WildernessLabs/Apiarium/Design/Sketches/Hive.png

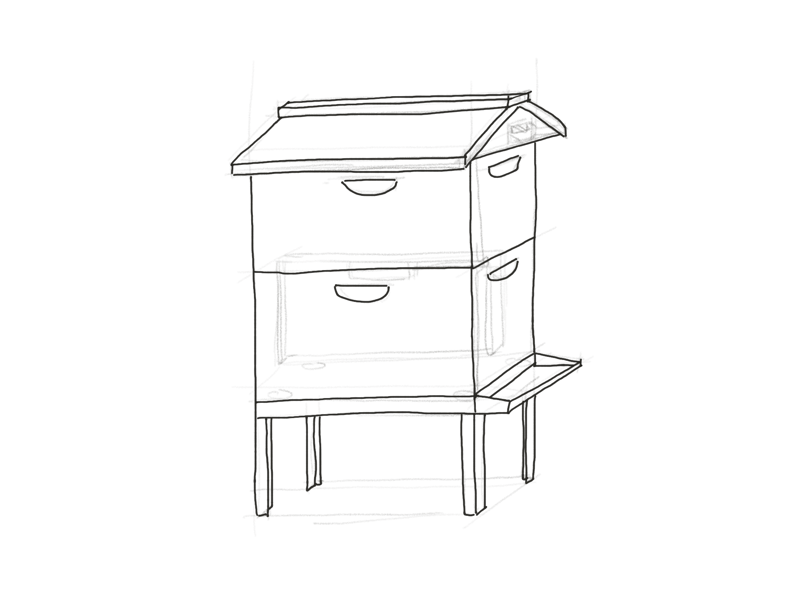
Design/Sketches/Hive.png
