WildernessLabs/Apiarium/Documentation/Photos/Enclosure_Bottom.jpg

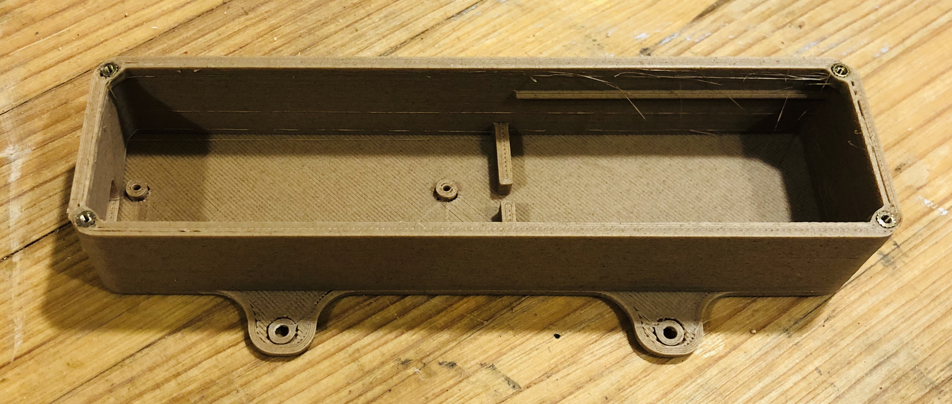
Documentation/Photos/Enclosure_Bottom.jpg
