WildernessLabs/Apiarium/Documentation/Photos/Enclosure_Lid.jpg

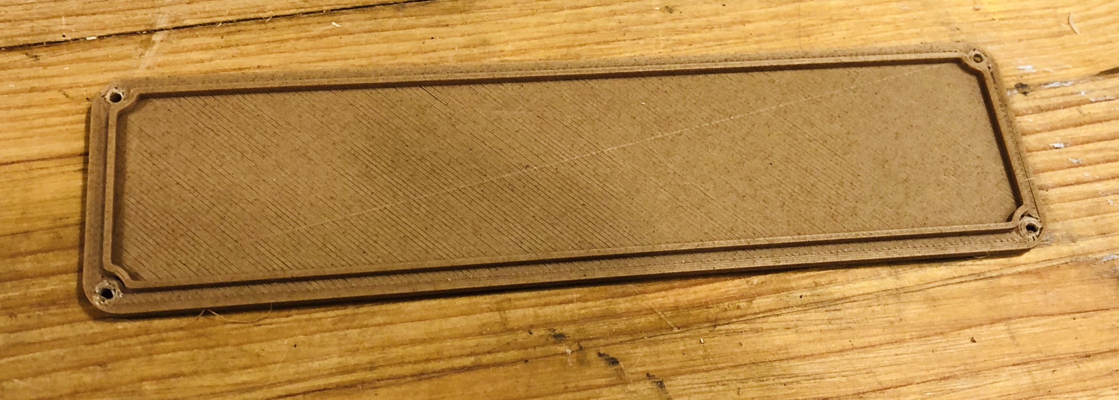
Documentation/Photos/Enclosure_Lid.jpg
