WildernessLabs/Apiarium/Documentation/Photos/M2_Heat-Set_Inserts.jpg

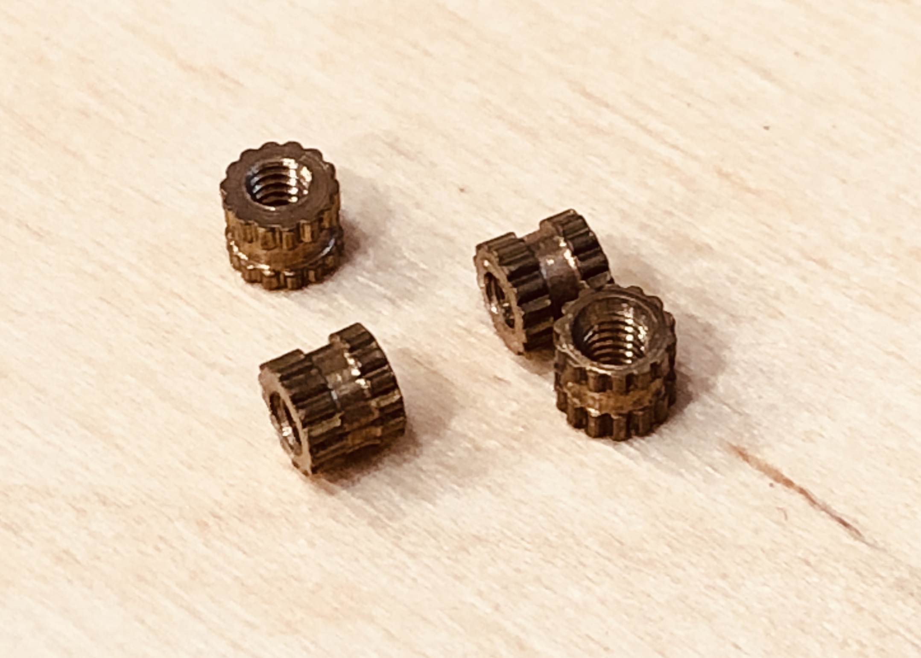
Documentation/Photos/M2_Heat-Set_Inserts.jpg
