WildernessLabs/Apiarium/Documentation/Photos/M2x4mm_Socket_Screws.jpg

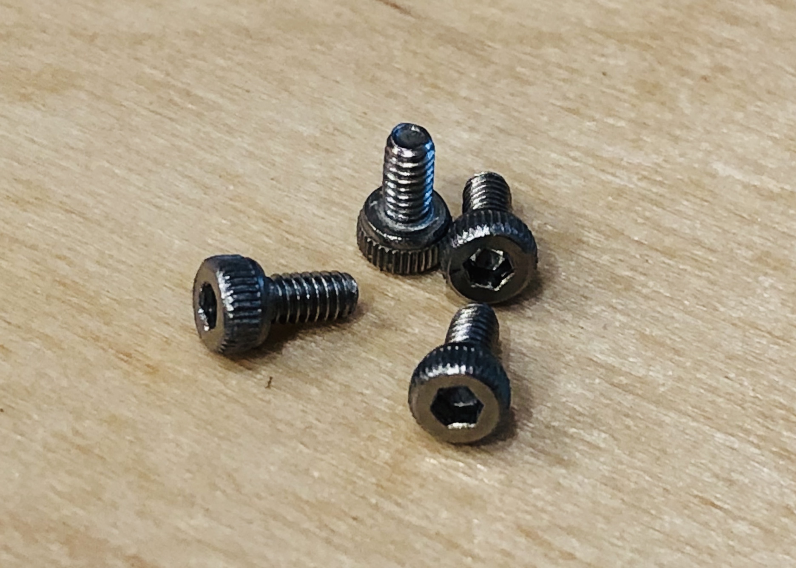
Documentation/Photos/M2x4mm_Socket_Screws.jpg
