WildernessLabs/Apiarium/Documentation/Photos/Meadow.jpg

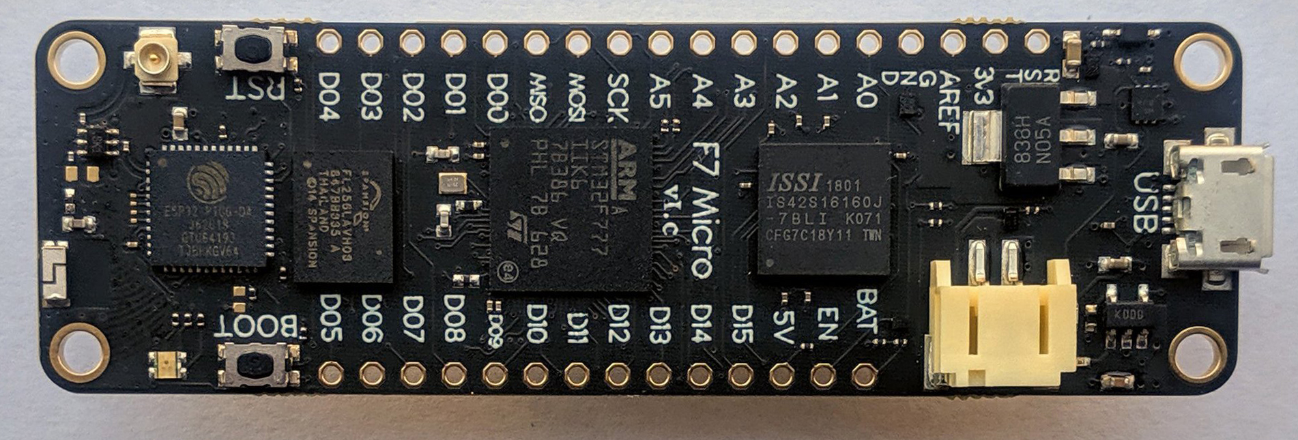
Documentation/Photos/Meadow.jpg
