WildernessLabs/Apiarium/Documentation/Photos/Si7021.jpg

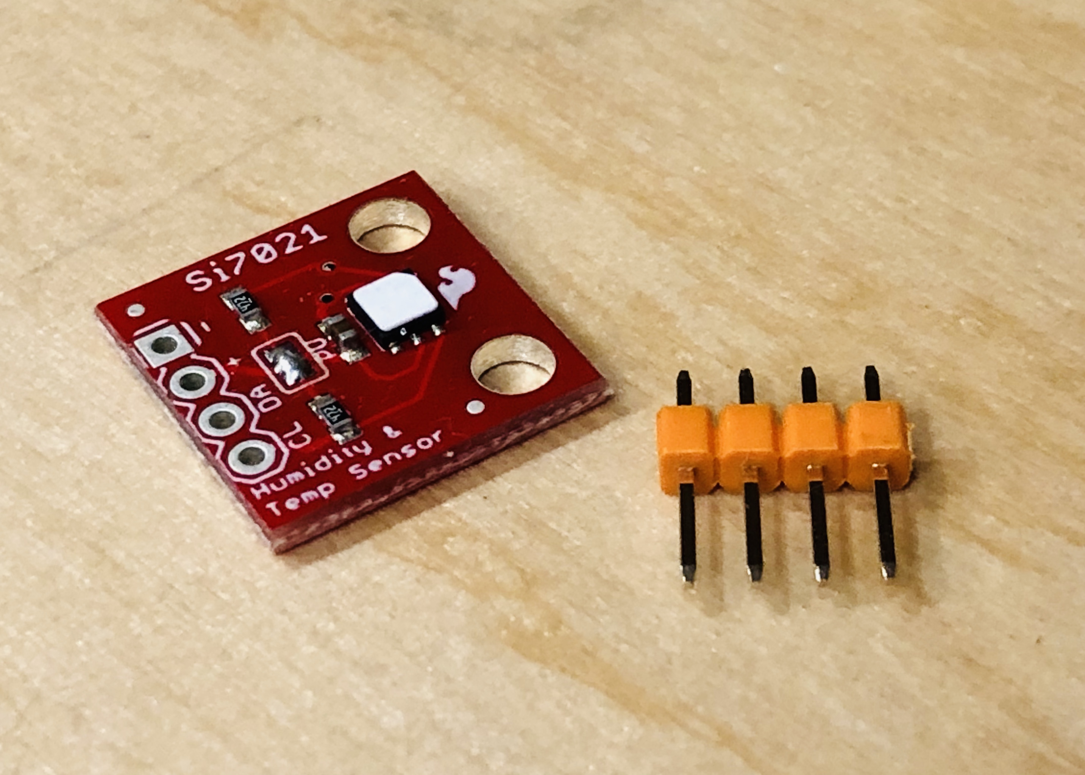
Documentation/Photos/Si7021.jpg
