WildernessLabs/Apiarium/Documentation/Photos/Wood_Screws.jpg

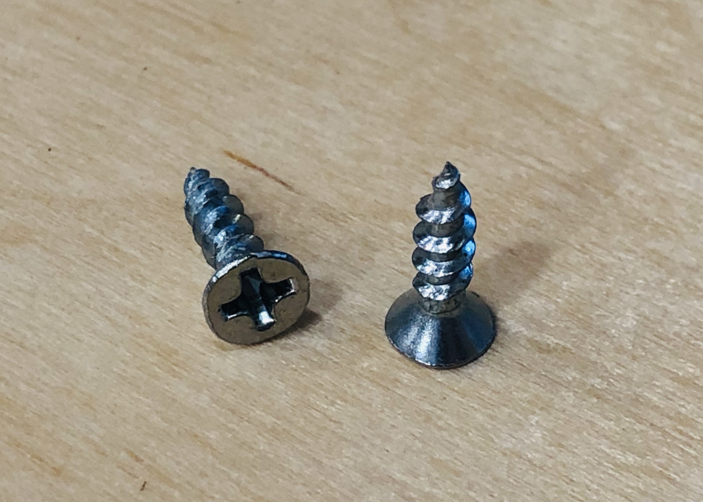
Documentation/Photos/Wood_Screws.jpg
